hansgaensbauer/Well-Monitor/pictures/20230929_115021.jpg

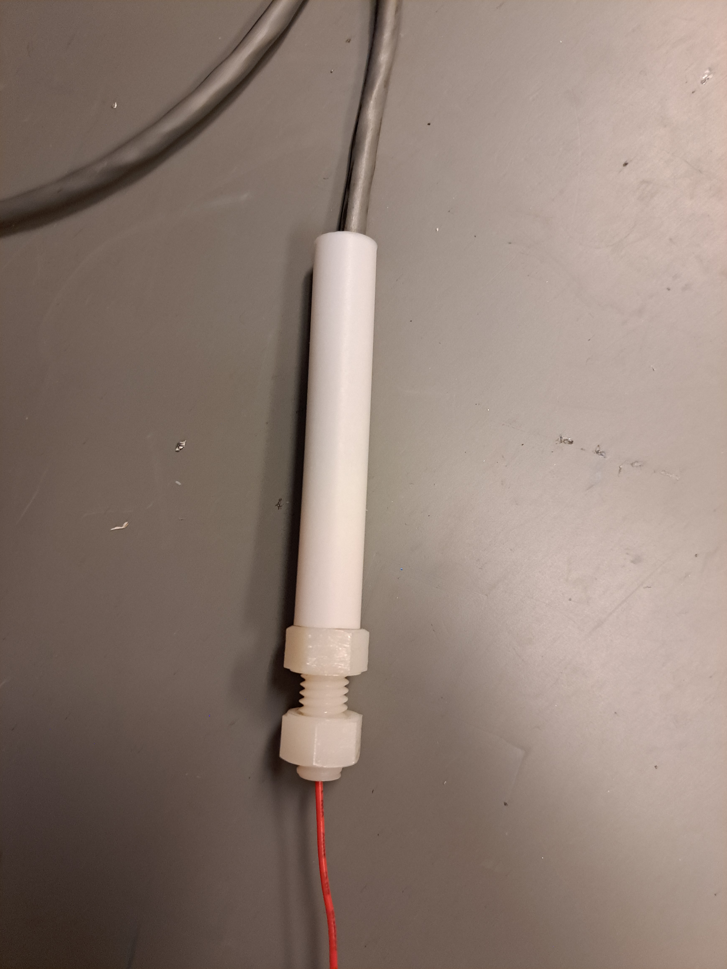
pictures/20230929_115021.jpg
