hansgaensbauer/Well-Monitor/pictures/20231022_133141.jpg

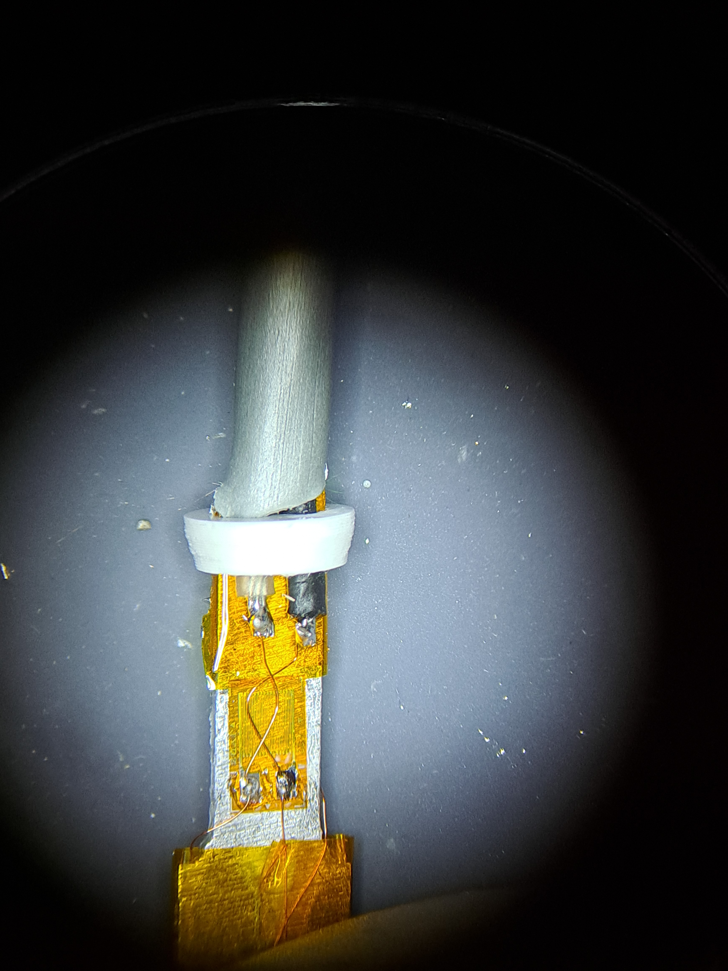
pictures/20231022_133141.jpg
