hansgaensbauer/Well-Monitor/pictures/20231111_165758.jpg

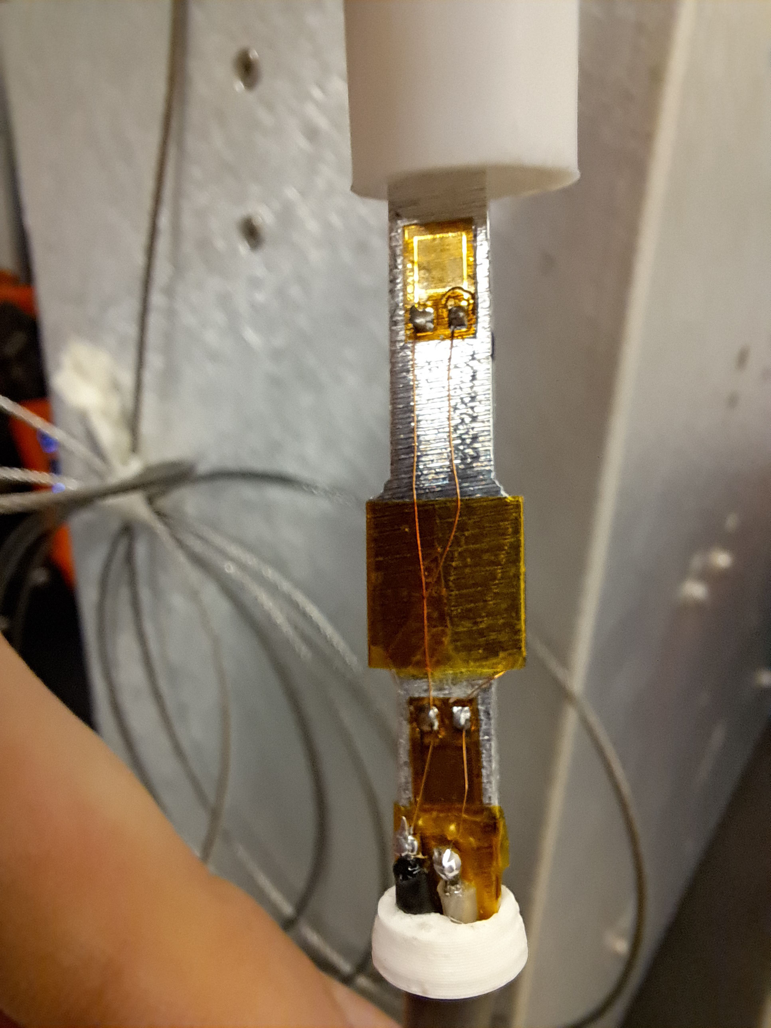
pictures/20231111_165758.jpg
