hansgaensbauer/Well-Monitor/pictures/20231111_165807.jpg

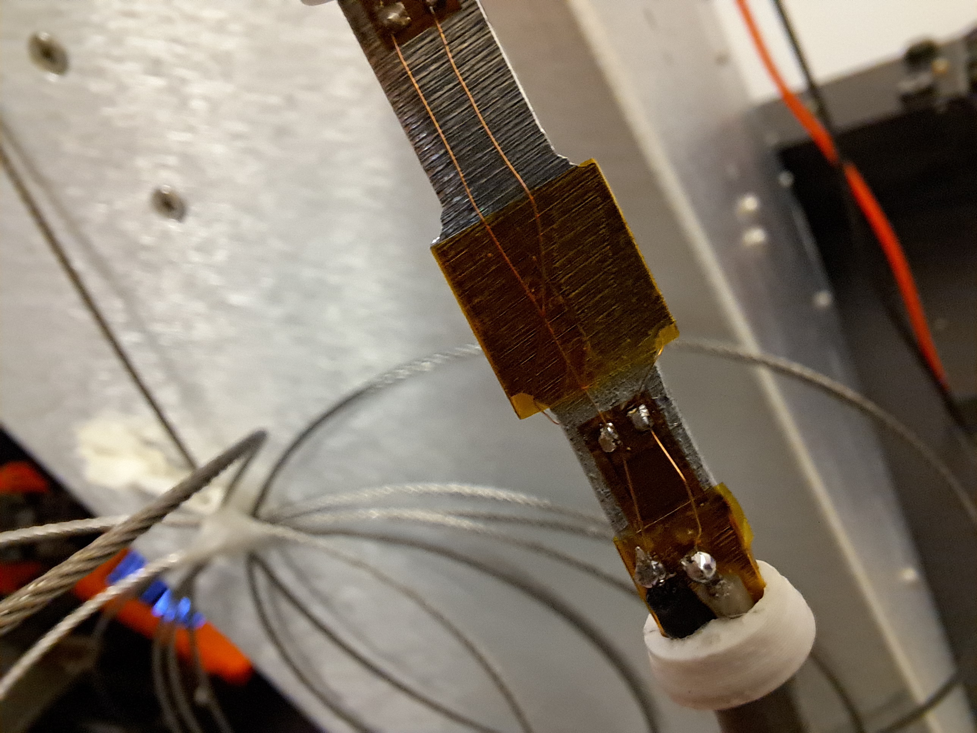
pictures/20231111_165807.jpg
