hansgaensbauer/Well-Monitor/pictures/20231111_165822.jpg

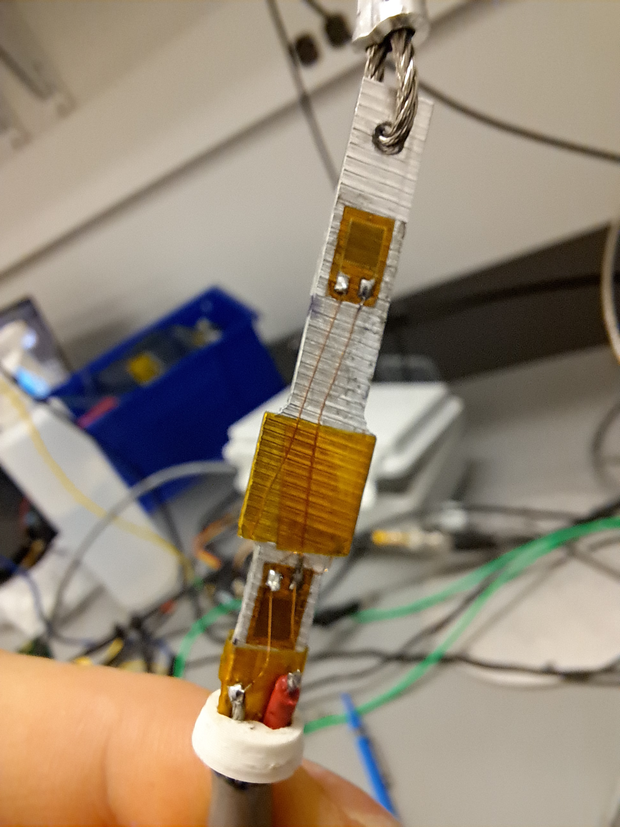
pictures/20231111_165822.jpg
