hansgaensbauer/Well-Monitor/pictures/20231112_120934.jpg

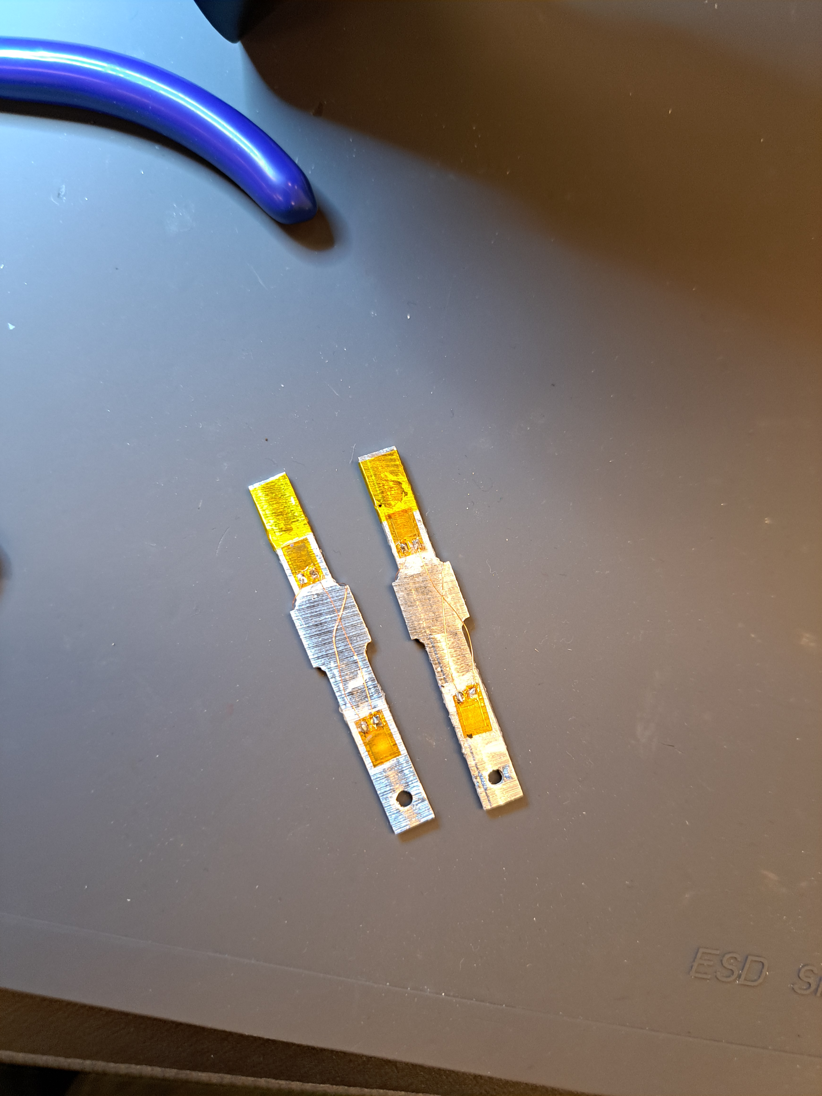
pictures/20231112_120934.jpg
