hansgaensbauer/Well-Monitor/pictures/20231112_131759.jpg

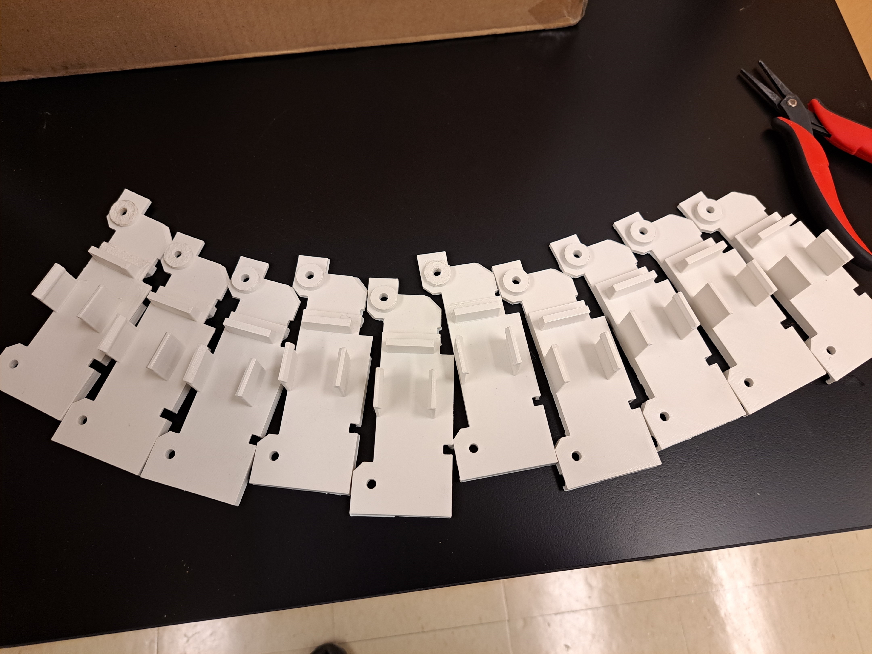
pictures/20231112_131759.jpg
