hansgaensbauer/Well-Monitor/pictures/20231118_135615.jpg

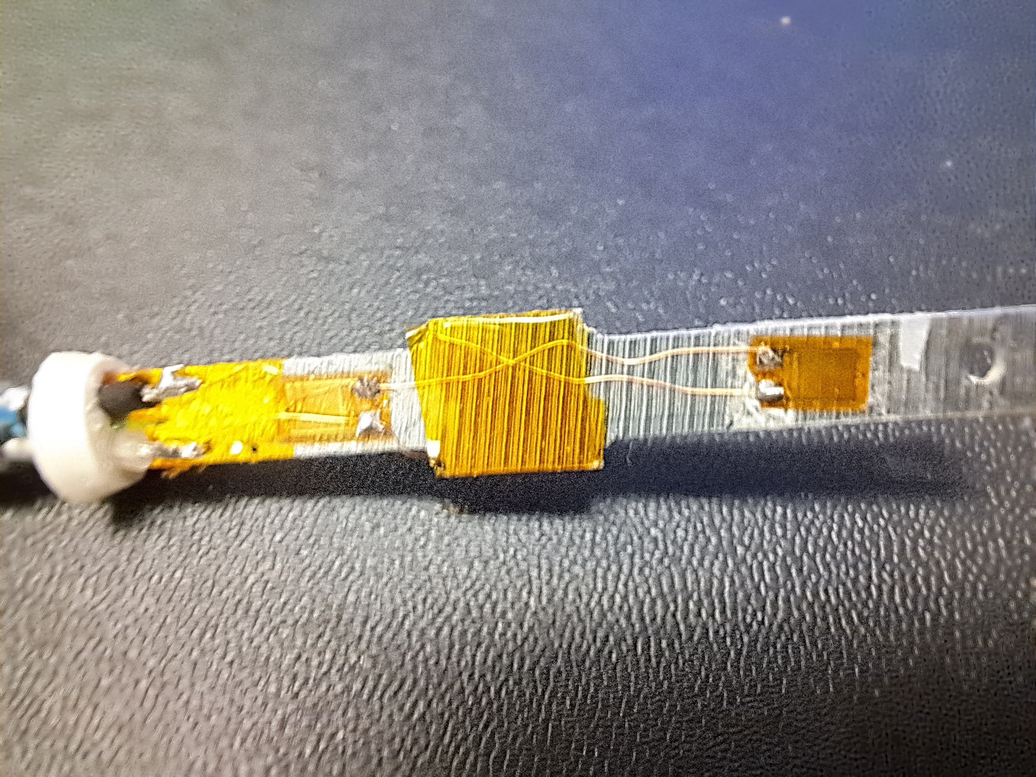
pictures/20231118_135615.jpg
