hansgaensbauer/Well-Monitor/pictures/20231118_135625.jpg

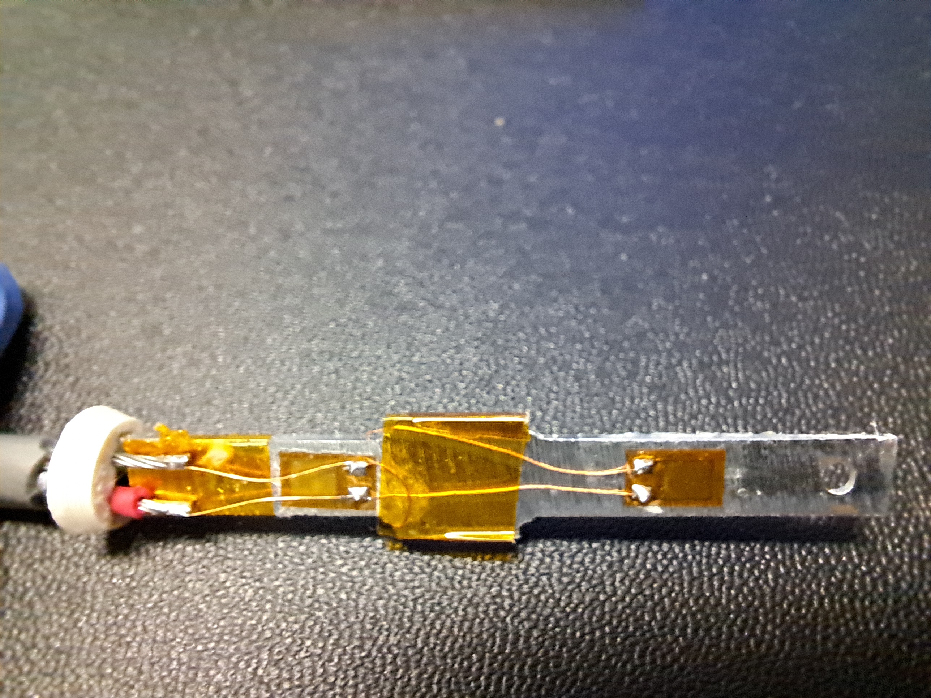
pictures/20231118_135625.jpg
