hansgaensbauer/Well-Monitor/pictures/20231118_142129.jpg

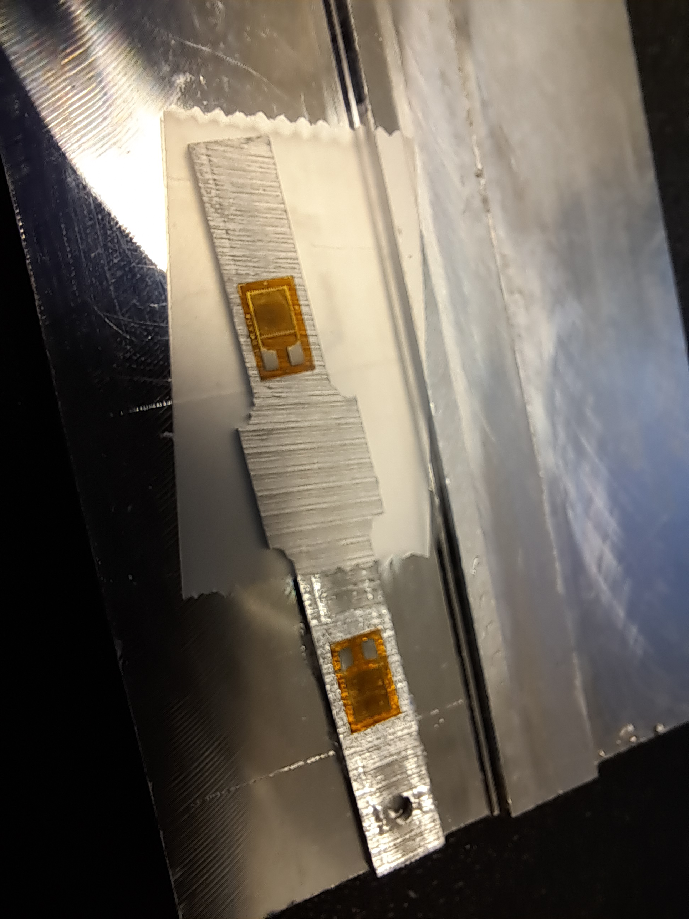
pictures/20231118_142129.jpg
