hansgaensbauer/Well-Monitor/pictures/20231118_192606.jpg

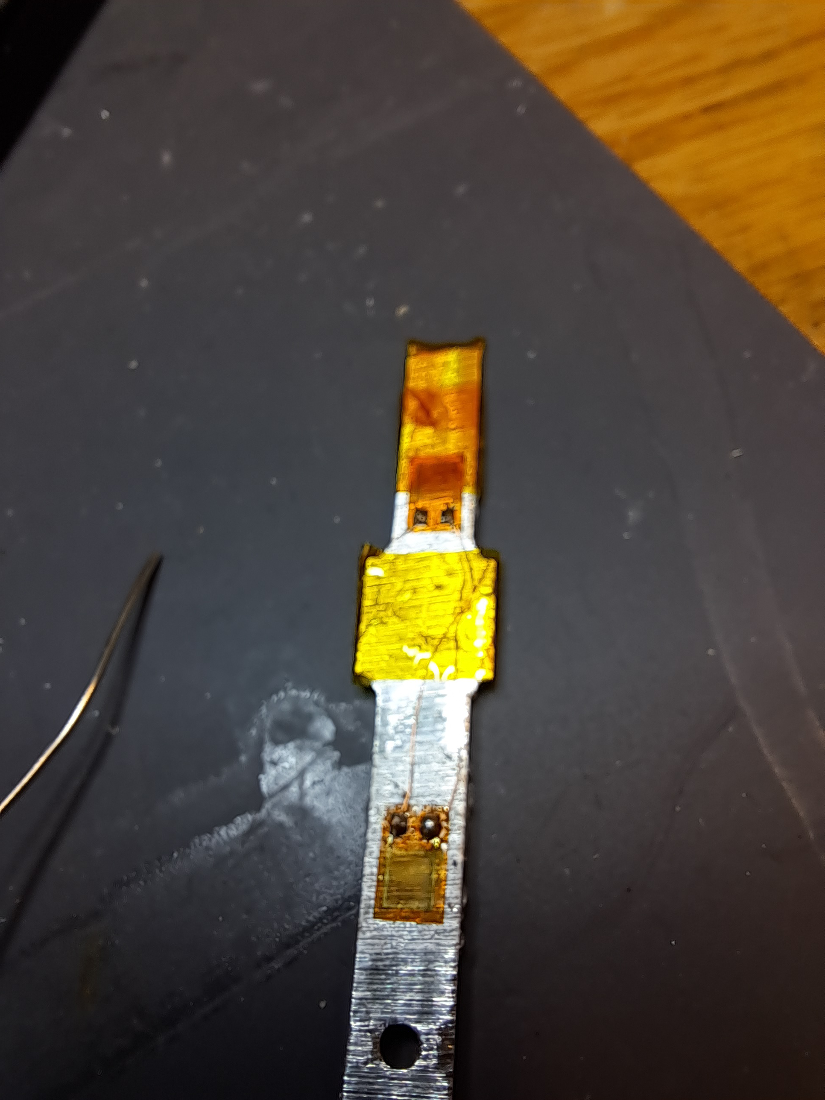
pictures/20231118_192606.jpg
