hansgaensbauer/Well-Monitor/pictures/20231119_173947.jpg

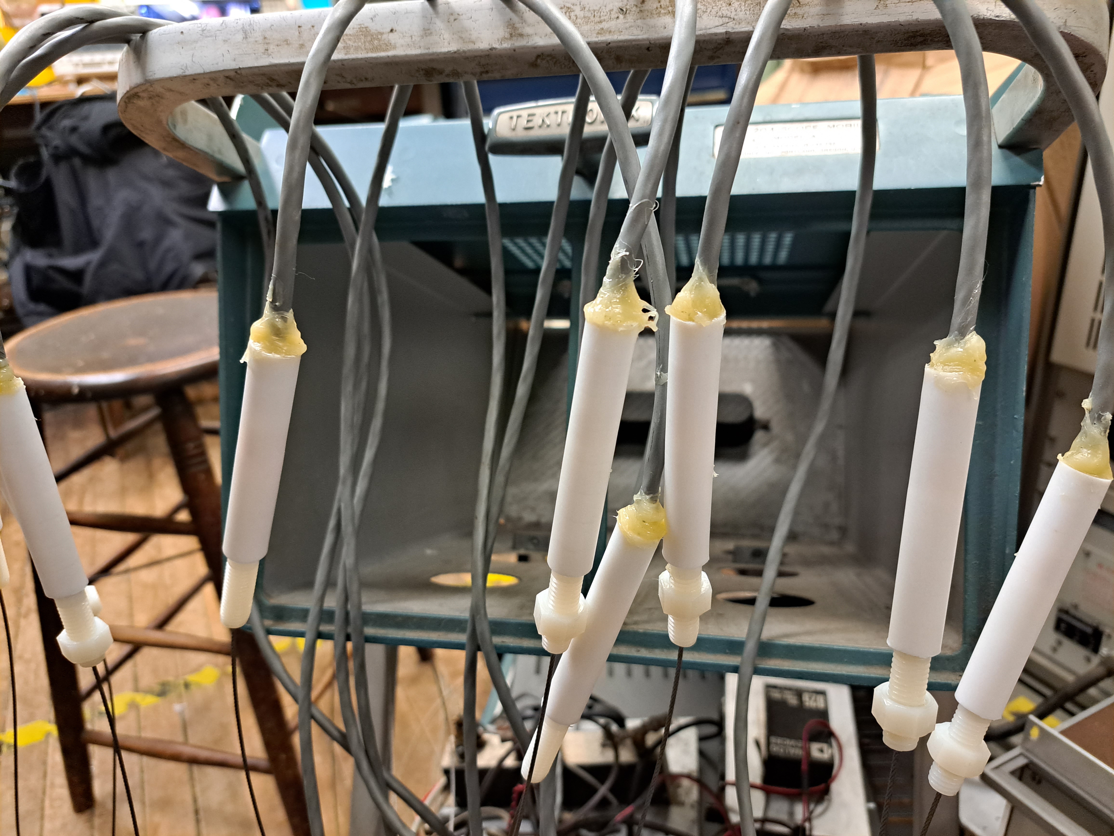
pictures/20231119_173947.jpg
