hansgaensbauer/Well-Monitor/pictures/20231202_200430.jpg

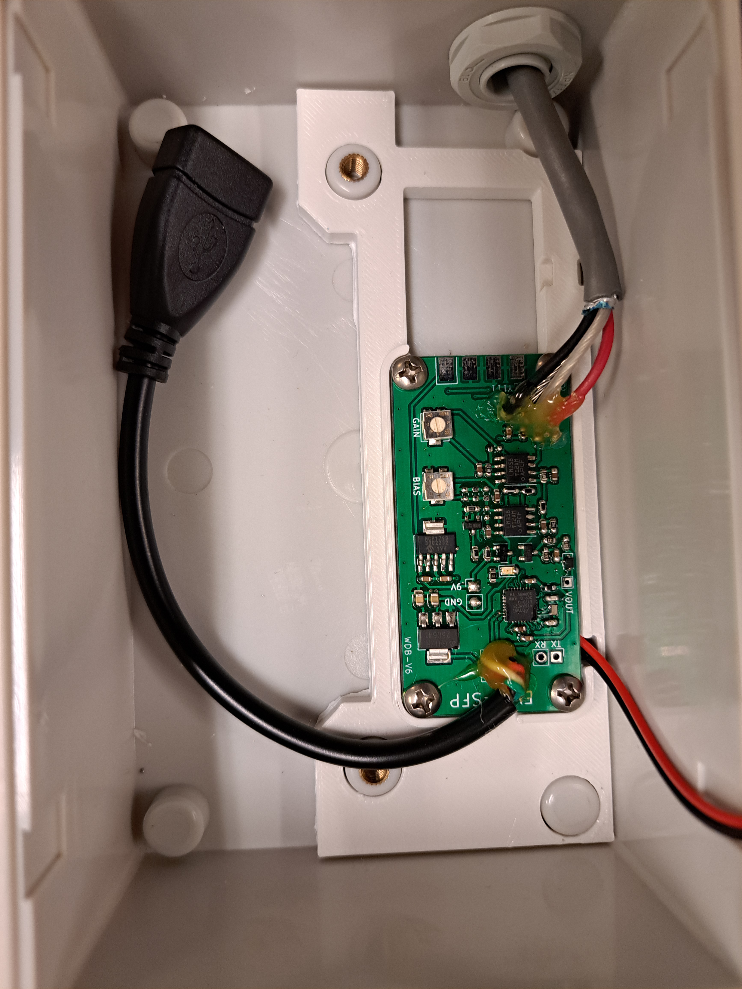
pictures/20231202_200430.jpg
