hansgaensbauer/Well-Monitor/pictures/20230524_154806.jpg

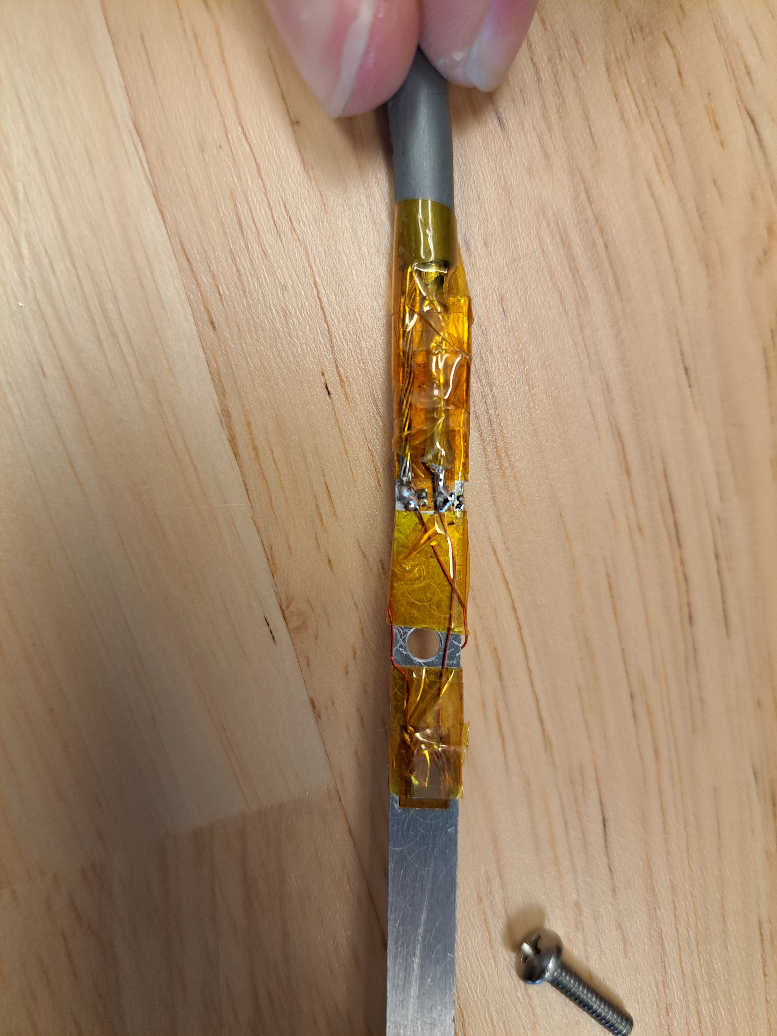
pictures/20230524_154806.jpg
