hansgaensbauer/Well-Monitor/pictures/20230524_154810.jpg

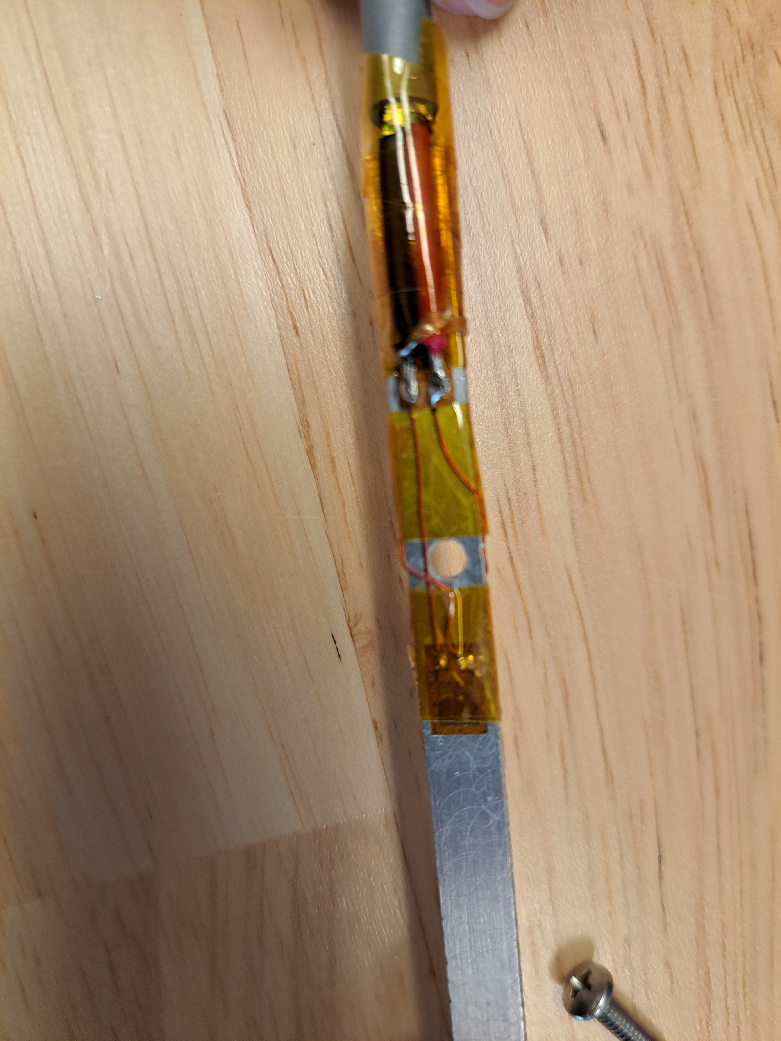
pictures/20230524_154810.jpg
