hansgaensbauer/Well-Monitor/pictures/20230808_111539.jpg

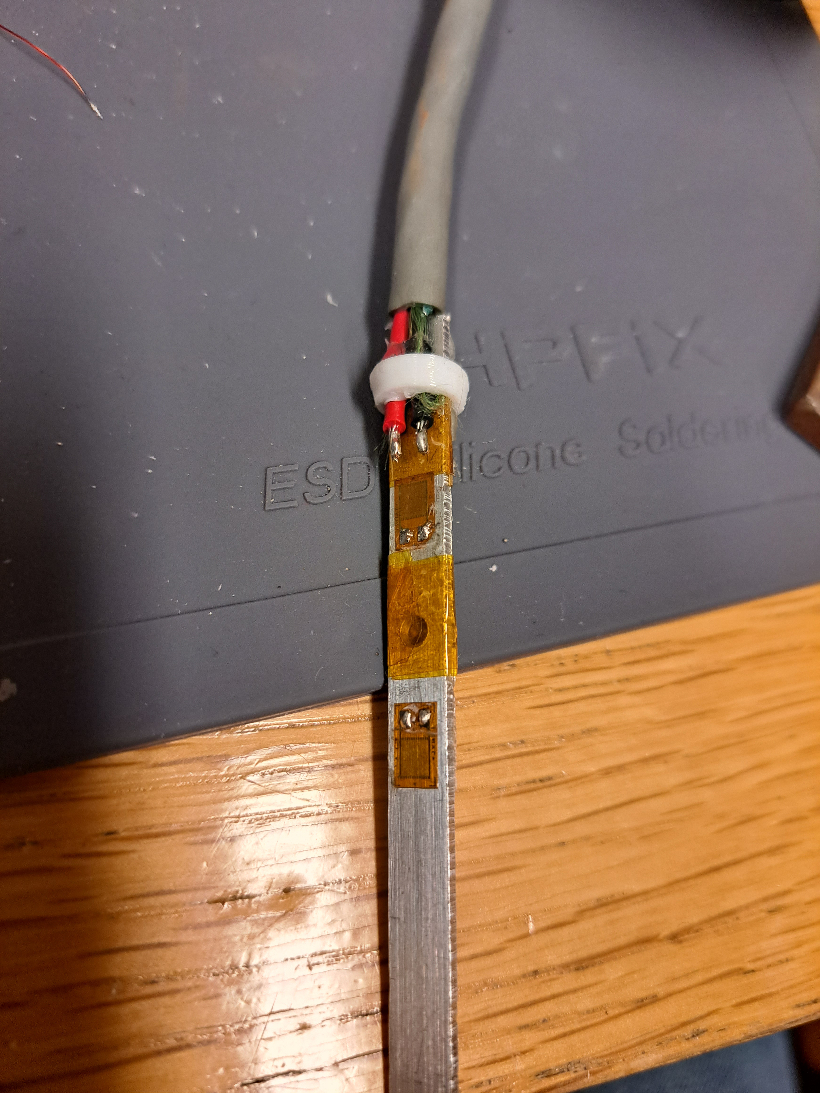
pictures/20230808_111539.jpg
