hansgaensbauer/Well-Monitor/pictures/20230929_114456.jpg

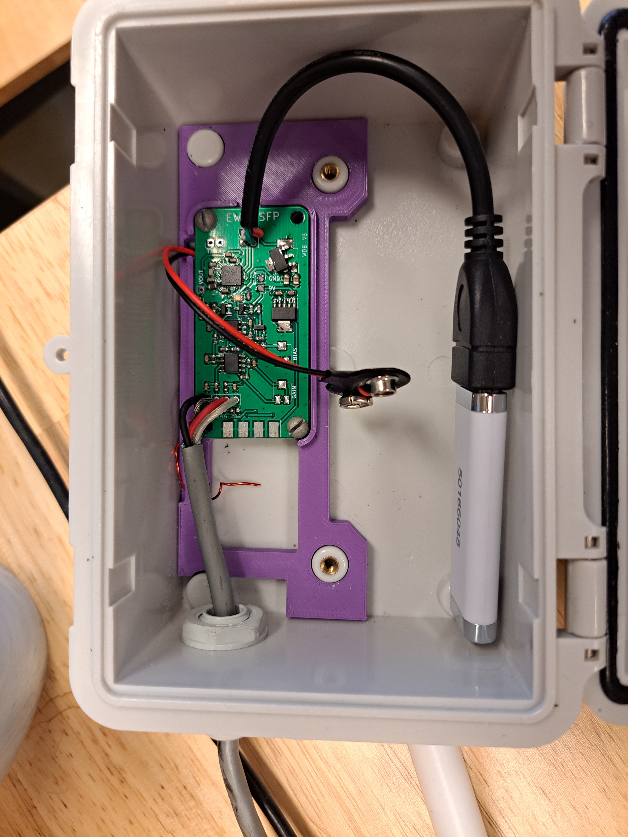
pictures/20230929_114456.jpg
