hansgaensbauer/Well-Monitor/pictures/20230929_114507.jpg

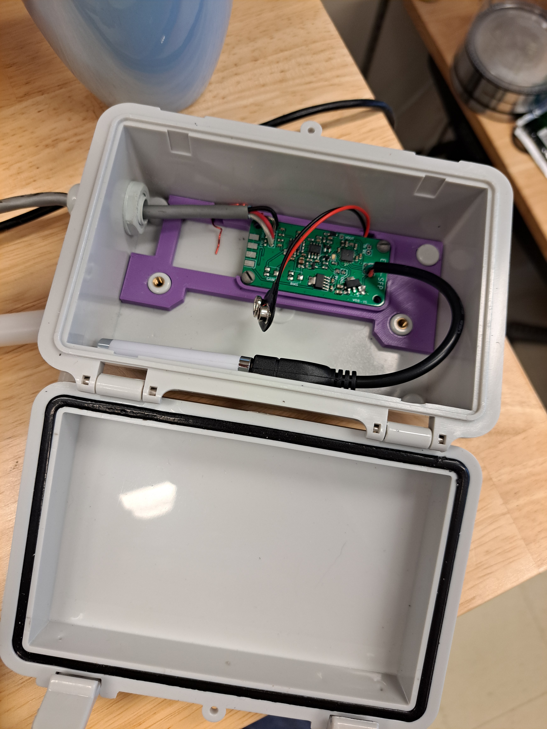
pictures/20230929_114507.jpg
