hansgaensbauer/Well-Monitor/pictures/20230929_114534.jpg

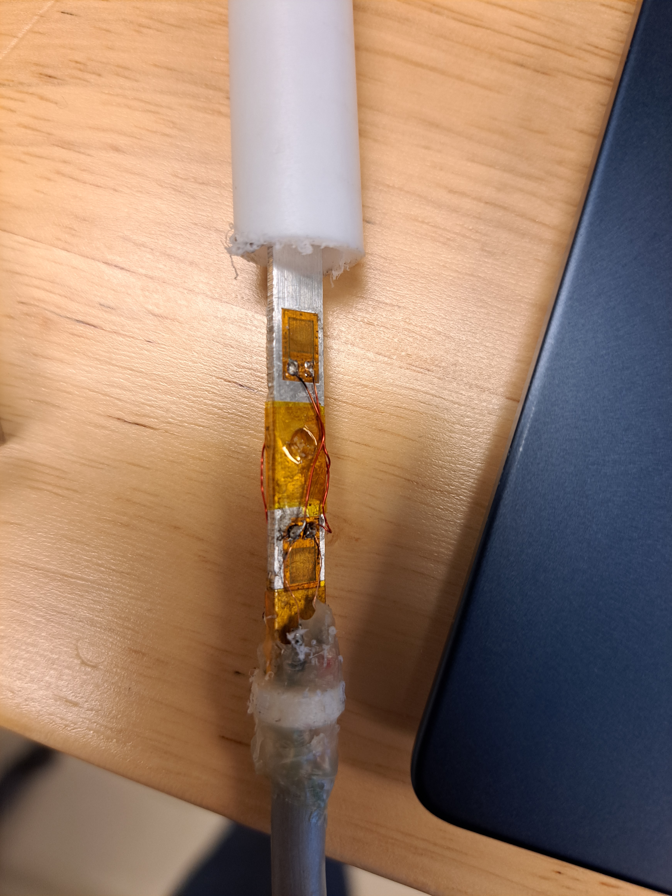
pictures/20230929_114534.jpg
