hansgaensbauer/Well-Monitor/pictures/20231111_173844.jpg

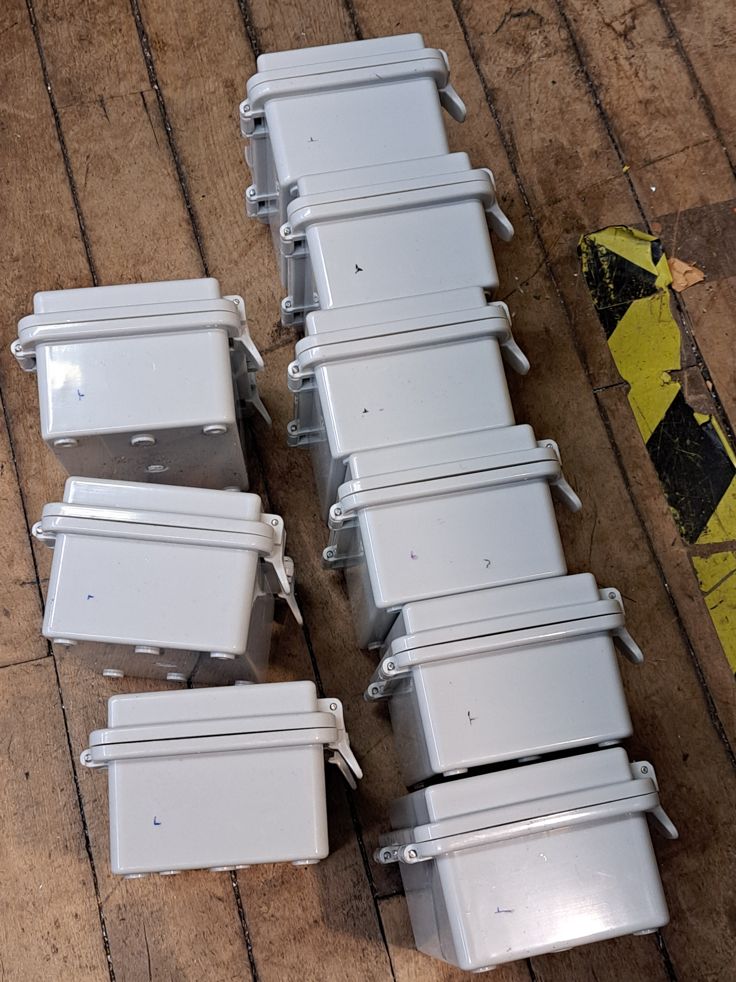
pictures/20231111_173844.jpg
