hansgaensbauer/Well-Monitor/pictures/20231119_142729.jpg

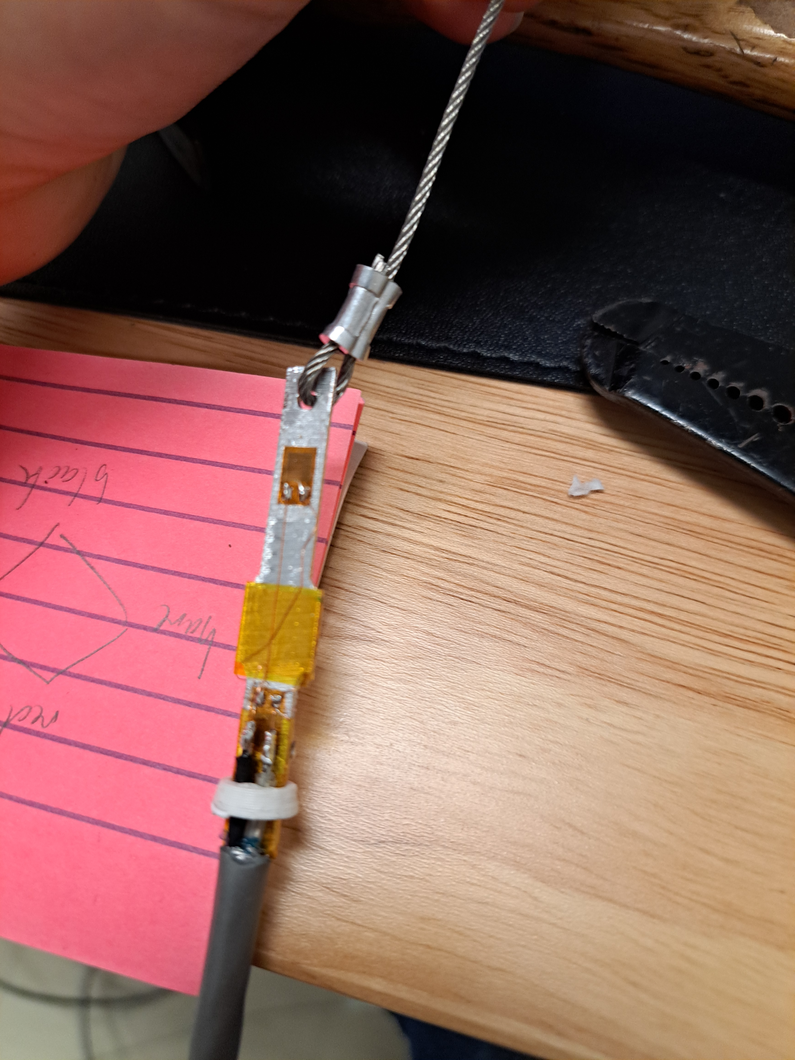
pictures/20231119_142729.jpg
