hansgaensbauer/Well-Monitor/pictures/20231202_200432.jpg

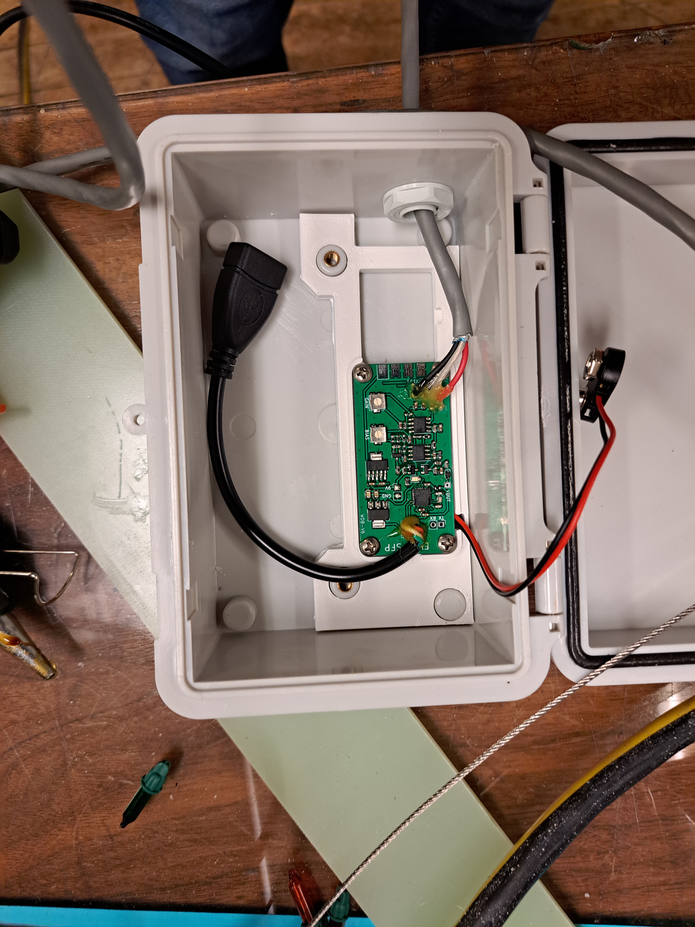
pictures/20231202_200432.jpg
